jerryok826/eFuse_voltmeter/Pictures/IMG_5857.jpeg

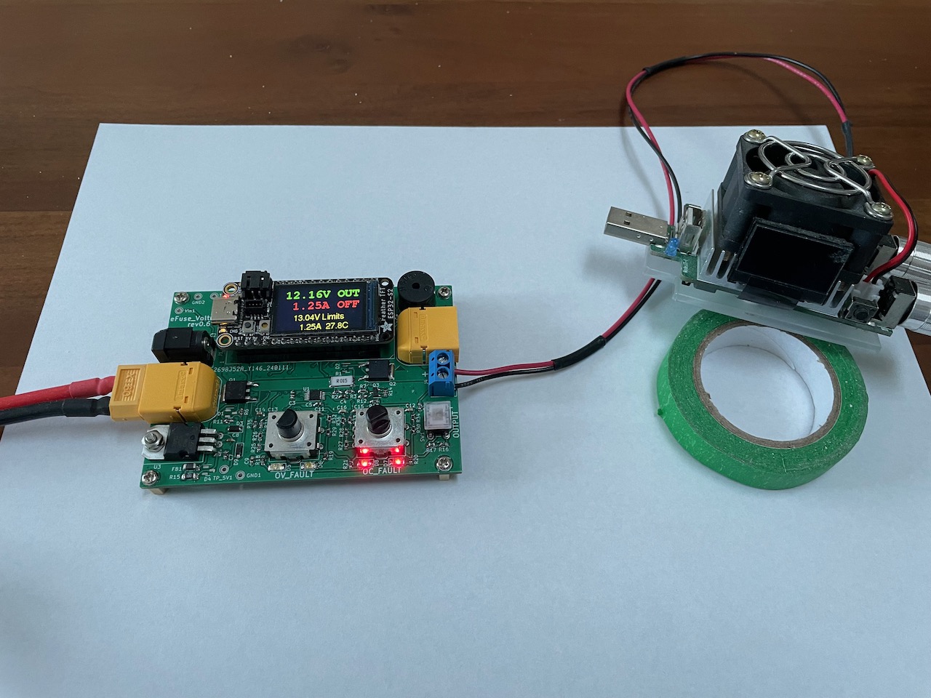
Pictures/IMG_5857.jpeg
